BoarderGamez/FrogBoard/pics/Screenshot 2025-12-14 181029.png

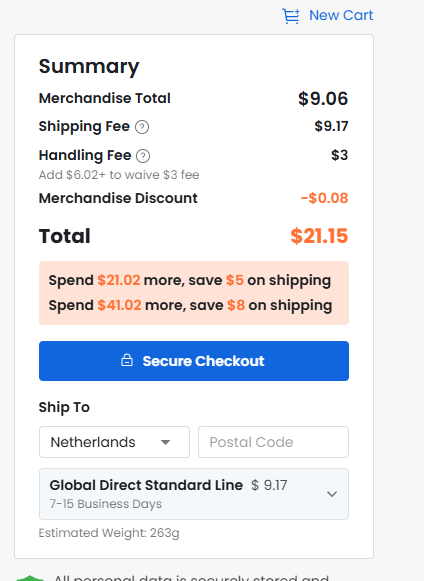
pics/Screenshot 2025-12-14 181029.png
