BoarderGamez/FrogBoard/pics/Screenshot 2025-12-14 181533.png

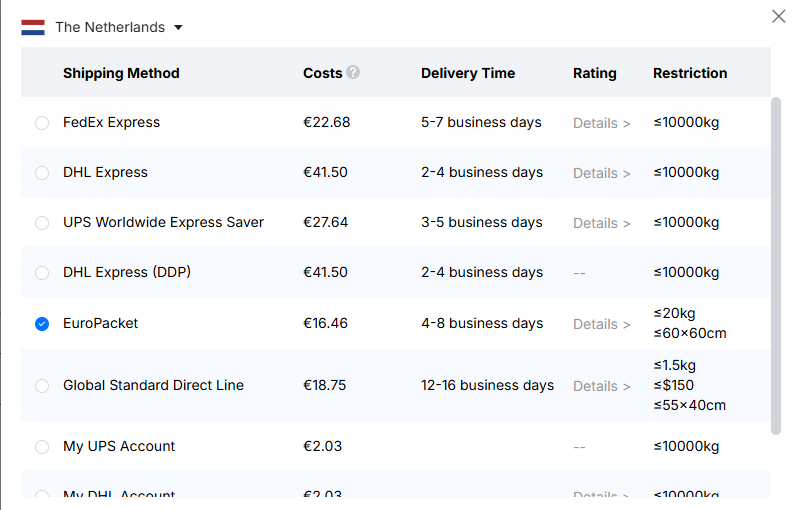
pics/Screenshot 2025-12-14 181533.png
